sini6a/pocketboard/assets/photos/1.jpg

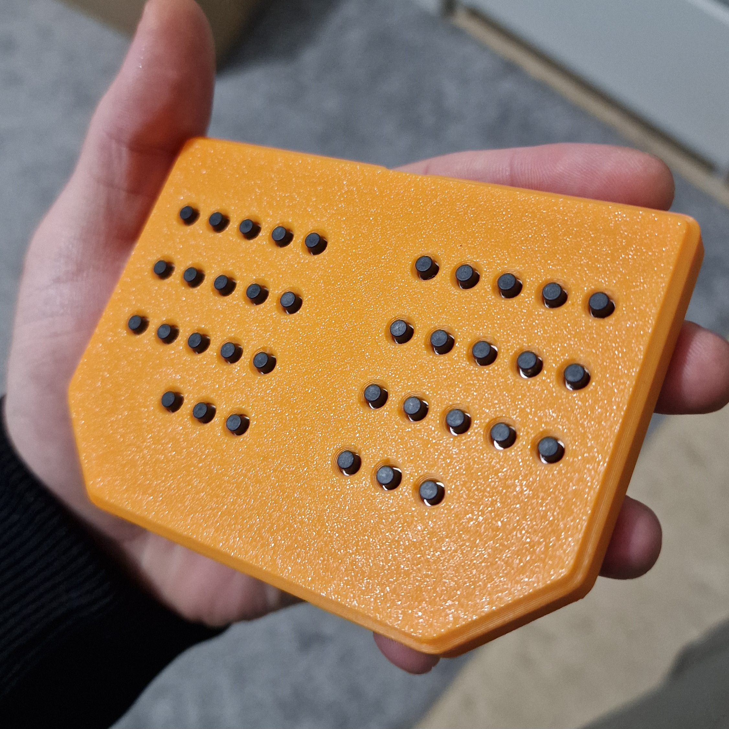
assets/photos/1.jpg
