sini6a/pocketboard/assets/photos/2.jpg

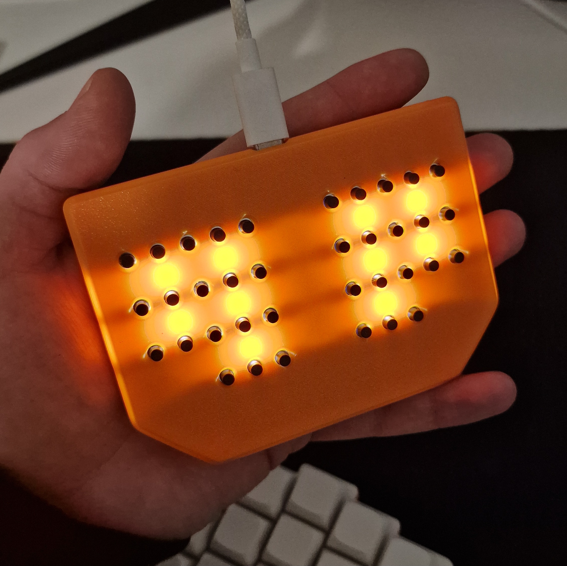
assets/photos/2.jpg
