sini6a/pocketboard/assets/photos/IMG_20250604_105842.jpg

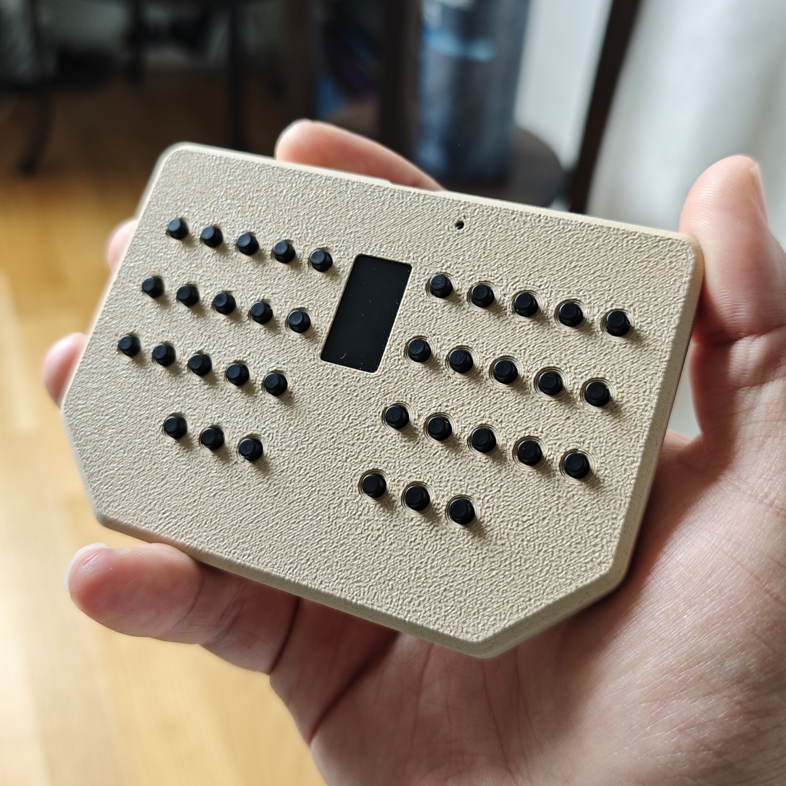
assets/photos/IMG_20250604_105842.jpg
